filipmu/Bat-Sonar/sonar/Documentation/doxygen/PIT_component.txt

/*!
  \page PIT PIT (Init_PIT)
**          This file implements the PIT (PIT) module initialization
**          according to the Peripheral Initialization settings, and
**          defines interrupt service routines prototypes.
**

- \subpage PIT_settings
- \subpage PIT_regs_overview  
- \subpage PIT_regs_details
- \ref PIT_module "Component documentation" 
\page PIT_regs_overview Registers Initialization Overview
This page contains the initialization values for the registers of the peripheral(s) configured
by the component. 
<table>
<tr><td colspan="4" class="ttitle1">PIT Initialization</td></tr>
<tr><td class="ttitle2">Address</td><td class="ttitle2">Register</td><td class="ttitle2">Register Value</td><td class="ttitle2">Register Description</td></tr>
<tr><td>0x40037000</td><td>PIT_MCR</td>
<td class="regNotResetVal">0x00000000</td>
 <td>PIT_MCR register, peripheral PIT.</td></tr>
<tr><td>0x4003710C</td><td>PIT_TFLG0</td>
<td class="regNotResetVal">0x00000001</td>
 <td>PIT_TFLG0 register, peripheral PIT.</td></tr>
<tr><td>0x4003711C</td><td>PIT_TFLG1</td>
<td class="regNotResetVal">0x00000001</td>
 <td>PIT_TFLG1 register, peripheral PIT.</td></tr>
<tr><td>0x4003712C</td><td>PIT_TFLG2</td>
<td class="regNotResetVal">0x00000001</td>
 <td>PIT_TFLG2 register, peripheral PIT.</td></tr>
<tr><td>0x4003713C</td><td>PIT_TFLG3</td>
<td class="regNotResetVal">0x00000001</td>
 <td>PIT_TFLG3 register, peripheral PIT.</td></tr>
<tr><td>0x40037108</td><td>PIT_TCTRL0</td>
<td class="regNotResetVal">0x00000002</td>
 <td>PIT_TCTRL0 register, peripheral PIT.</td></tr>
<tr><td>0x40037118</td><td>PIT_TCTRL1</td>
<td class="regResetVal">0x00000000</td>
 <td>PIT_TCTRL1 register, peripheral PIT.</td></tr>
<tr><td>0x40037128</td><td>PIT_TCTRL2</td>
<td class="regResetVal">0x00000000</td>
 <td>PIT_TCTRL2 register, peripheral PIT.</td></tr>
<tr><td>0x40037138</td><td>PIT_TCTRL3</td>
<td class="regResetVal">0x00000000</td>
 <td>PIT_TCTRL3 register, peripheral PIT.</td></tr>
<tr><td>0x40037100</td><td>PIT_LDVAL0</td>
<td class="regNotResetVal">0x000003E7</td>
 <td>PIT_LDVAL0 register, peripheral PIT.</td></tr>
<tr><td>0x40037110</td><td>PIT_LDVAL1</td>
<td class="regResetVal">0x00000000</td>
 <td>PIT_LDVAL1 register, peripheral PIT.</td></tr>
<tr><td>0x40037120</td><td>PIT_LDVAL2</td>
<td class="regResetVal">0x00000000</td>
 <td>PIT_LDVAL2 register, peripheral PIT.</td></tr>
<tr><td>0x40037130</td><td>PIT_LDVAL3</td>
<td class="regResetVal">0x00000000</td>
 <td>PIT_LDVAL3 register, peripheral PIT.</td></tr>
</table>
Color Denotes Reset Value
<br/>
\page PIT_regs_details Register Initialization Details
This page contains detailed description of initialization values for the 
registers of the peripheral(s) configured by the component. 

<div class="reghdr1">PIT_MCR</div>
<div class="regdiag">
<table class="regtbl">
<tr class="trd1r">
<td class="trd1c">Bit</td><td>31</td><td>30</td><td>29</td><td>28</td><td>27</td><td>26</td><td>25</td><td>24</td><td>23</td>
<td>22</td><td>21</td><td>20</td><td>19</td><td>18</td><td>17</td><td>16</td>
</tr>
<tr>
<td class="trd1c">R</td><td colspan="1" rowspan="2">-</td><td colspan="1" rowspan="2">-</td><td colspan="1" rowspan="2">-</td>
<td colspan="1" rowspan="2">-</td><td colspan="1" rowspan="2">-</td><td colspan="1" rowspan="2">-</td>
<td colspan="1" rowspan="2">-</td><td colspan="1" rowspan="2">-</td><td colspan="1" rowspan="2">-</td>
<td colspan="1" rowspan="2">-</td><td colspan="1" rowspan="2">-</td><td colspan="1" rowspan="2">-</td>
<td colspan="1" rowspan="2">-</td><td colspan="1" rowspan="2">-</td><td colspan="1" rowspan="2">-</td>
<td colspan="1" rowspan="2">-</td>
</tr>
<tr>
<td class="trd1c">W</td>
</tr>
<tr class="trd1r">
<td class="trd1c">Reset</td><td>0</td><td>0</td><td>0</td><td>0</td><td>0</td><td>0</td><td>0</td><td>0</td><td>0</td><td>0</td>
<td>0</td><td>0</td><td>0</td><td>0</td><td>0</td><td>0</td>
</tr>
</table>
<table class="regtbl">
<tr class="trd1r">
<td class="trd1c">Bit</td><td>15</td><td>14</td><td>13</td><td>12</td><td>11</td><td>10</td><td>9</td><td>8</td><td>7</td>
<td>6</td><td>5</td><td>4</td><td>3</td><td>2</td><td>1</td><td>0</td>
</tr>
<tr>
<td class="trd1c">R</td><td colspan="1" rowspan="2">-</td><td colspan="1" rowspan="2">-</td><td colspan="1" rowspan="2">-</td>
<td colspan="1" rowspan="2">-</td><td colspan="1" rowspan="2">-</td><td colspan="1" rowspan="2">-</td>
<td colspan="1" rowspan="2">-</td><td colspan="1" rowspan="2">-</td><td colspan="1" rowspan="2">-</td>
<td colspan="1" rowspan="2">-</td><td colspan="1" rowspan="2">-</td><td colspan="1" rowspan="2">-</td>
<td colspan="1" rowspan="2">-</td><td colspan="1" rowspan="2">-</td><td colspan="1" rowspan="2">MDIS</td>
<td colspan="1" rowspan="2">FRZ</td>
</tr>
<tr>
<td class="trd1c">W</td>
</tr>
<tr class="trd1r">
<td class="trd1c">Reset</td><td>0</td><td>0</td><td>0</td><td>0</td><td>0</td><td>0</td><td>0</td><td>0</td><td>0</td><td>0</td>
<td>0</td><td>0</td><td>0</td><td>1</td><td>1</td><td>0</td>
</tr>
</table>
        
</div>
<table class="regtbl2"><tr><td class="trowtit" colspan="2">Address</td><td colspan="2">0x40037000</td></tr>
<tr class="trowtit"><td  class="trowtit" colspan="2">Initial value</td><td colspan="2">0x00000000</td></tr>
<tr class="trowtit"><td  class="trowtit" colspan="2">After-reset value</td><td colspan="2">0x00000006</td></tr>
<tr><td class="ttitle2">Bit</td><td class="ttitle2">Field</td><td class="ttitle2">Value</td><td class="ttitle2">Description</td></tr>
<tr><td>1</td><td>MDIS</td><td>0x00</td><td>Module Disable - (PIT section)</td>
<tr><td>0</td><td>FRZ</td><td>0x00</td><td>Freeze</td>
</tr></table>
<div class="reghdr1">PIT_TFLG0</div>
<div class="regdiag">
<table class="regtbl">
<tr class="trd1r">
<td class="trd1c">Bit</td><td>31</td><td>30</td><td>29</td><td>28</td><td>27</td><td>26</td><td>25</td><td>24</td><td>23</td>
<td>22</td><td>21</td><td>20</td><td>19</td><td>18</td><td>17</td><td>16</td>
</tr>
<tr>
<td class="trd1c">R</td><td colspan="1" rowspan="2">-</td><td colspan="1" rowspan="2">-</td><td colspan="1" rowspan="2">-</td>
<td colspan="1" rowspan="2">-</td><td colspan="1" rowspan="2">-</td><td colspan="1" rowspan="2">-</td>
<td colspan="1" rowspan="2">-</td><td colspan="1" rowspan="2">-</td><td colspan="1" rowspan="2">-</td>
<td colspan="1" rowspan="2">-</td><td colspan="1" rowspan="2">-</td><td colspan="1" rowspan="2">-</td>
<td colspan="1" rowspan="2">-</td><td colspan="1" rowspan="2">-</td><td colspan="1" rowspan="2">-</td>
<td colspan="1" rowspan="2">-</td>
</tr>
<tr>
<td class="trd1c">W</td>
</tr>
<tr class="trd1r">
<td class="trd1c">Reset</td><td>0</td><td>0</td><td>0</td><td>0</td><td>0</td><td>0</td><td>0</td><td>0</td><td>0</td><td>0</td>
<td>0</td><td>0</td><td>0</td><td>0</td><td>0</td><td>0</td>
</tr>
</table>
<table class="regtbl">
<tr class="trd1r">
<td class="trd1c">Bit</td><td>15</td><td>14</td><td>13</td><td>12</td><td>11</td><td>10</td><td>9</td><td>8</td><td>7</td>
<td>6</td><td>5</td><td>4</td><td>3</td><td>2</td><td>1</td><td>0</td>
</tr>
<tr>
<td class="trd1c">R</td><td colspan="1" rowspan="2">-</td><td colspan="1" rowspan="2">-</td><td colspan="1" rowspan="2">-</td>
<td colspan="1" rowspan="2">-</td><td colspan="1" rowspan="2">-</td><td colspan="1" rowspan="2">-</td>
<td colspan="1" rowspan="2">-</td><td colspan="1" rowspan="2">-</td><td colspan="1" rowspan="2">-</td>
<td colspan="1" rowspan="2">-</td><td colspan="1" rowspan="2">-</td><td colspan="1" rowspan="2">-</td>
<td colspan="1" rowspan="2">-</td><td colspan="1" rowspan="2">-</td><td colspan="1" rowspan="2">-</td>
<td colspan="1" rowspan="2">TIF</td>
</tr>
<tr>
<td class="trd1c">W</td>
</tr>
<tr class="trd1r">
<td class="trd1c">Reset</td><td>0</td><td>0</td><td>0</td><td>0</td><td>0</td><td>0</td><td>0</td><td>0</td><td>0</td><td>0</td>
<td>0</td><td>0</td><td>0</td><td>0</td><td>0</td><td>0</td>
</tr>
</table>
        
</div>
<table class="regtbl2"><tr><td class="trowtit" colspan="2">Address</td><td colspan="2">0x4003710C</td></tr>
<tr class="trowtit"><td  class="trowtit" colspan="2">Initial value</td><td colspan="2">0x00000001</td></tr>
<tr class="trowtit"><td  class="trowtit" colspan="2">After-reset value</td><td colspan="2">0x00000000</td></tr>
<tr><td class="ttitle2">Bit</td><td class="ttitle2">Field</td><td class="ttitle2">Value</td><td class="ttitle2">Description</td></tr>
<tr><td>0</td><td>TIF</td><td>0x01</td><td>Timer Interrupt Flag</td>
</tr></table>
<div class="reghdr1">PIT_TFLG1</div>
<div class="regdiag">
<table class="regtbl">
<tr class="trd1r">
<td class="trd1c">Bit</td><td>31</td><td>30</td><td>29</td><td>28</td><td>27</td><td>26</td><td>25</td><td>24</td><td>23</td>
<td>22</td><td>21</td><td>20</td><td>19</td><td>18</td><td>17</td><td>16</td>
</tr>
<tr>
<td class="trd1c">R</td><td colspan="1" rowspan="2">-</td><td colspan="1" rowspan="2">-</td><td colspan="1" rowspan="2">-</td>
<td colspan="1" rowspan="2">-</td><td colspan="1" rowspan="2">-</td><td colspan="1" rowspan="2">-</td>
<td colspan="1" rowspan="2">-</td><td colspan="1" rowspan="2">-</td><td colspan="1" rowspan="2">-</td>
<td colspan="1" rowspan="2">-</td><td colspan="1" rowspan="2">-</td><td colspan="1" rowspan="2">-</td>
<td colspan="1" rowspan="2">-</td><td colspan="1" rowspan="2">-</td><td colspan="1" rowspan="2">-</td>
<td colspan="1" rowspan="2">-</td>
</tr>
<tr>
<td class="trd1c">W</td>
</tr>
<tr class="trd1r">
<td class="trd1c">Reset</td><td>0</td><td>0</td><td>0</td><td>0</td><td>0</td><td>0</td><td>0</td><td>0</td><td>0</td><td>0</td>
<td>0</td><td>0</td><td>0</td><td>0</td><td>0</td><td>0</td>
</tr>
</table>
<table class="regtbl">
<tr class="trd1r">
<td class="trd1c">Bit</td><td>15</td><td>14</td><td>13</td><td>12</td><td>11</td><td>10</td><td>9</td><td>8</td><td>7</td>
<td>6</td><td>5</td><td>4</td><td>3</td><td>2</td><td>1</td><td>0</td>
</tr>
<tr>
<td class="trd1c">R</td><td colspan="1" rowspan="2">-</td><td colspan="1" rowspan="2">-</td><td colspan="1" rowspan="2">-</td>
<td colspan="1" rowspan="2">-</td><td colspan="1" rowspan="2">-</td><td colspan="1" rowspan="2">-</td>
<td colspan="1" rowspan="2">-</td><td colspan="1" rowspan="2">-</td><td colspan="1" rowspan="2">-</td>
<td colspan="1" rowspan="2">-</td><td colspan="1" rowspan="2">-</td><td colspan="1" rowspan="2">-</td>
<td colspan="1" rowspan="2">-</td><td colspan="1" rowspan="2">-</td><td colspan="1" rowspan="2">-</td>
<td colspan="1" rowspan="2">TIF</td>
</tr>
<tr>
<td class="trd1c">W</td>
</tr>
<tr class="trd1r">
<td class="trd1c">Reset</td><td>0</td><td>0</td><td>0</td><td>0</td><td>0</td><td>0</td><td>0</td><td>0</td><td>0</td><td>0</td>
<td>0</td><td>0</td><td>0</td><td>0</td><td>0</td><td>0</td>
</tr>
</table>
        
</div>
<table class="regtbl2"><tr><td class="trowtit" colspan="2">Address</td><td colspan="2">0x4003711C</td></tr>
<tr class="trowtit"><td  class="trowtit" colspan="2">Initial value</td><td colspan="2">0x00000001</td></tr>
<tr class="trowtit"><td  class="trowtit" colspan="2">After-reset value</td><td colspan="2">0x00000000</td></tr>
<tr><td class="ttitle2">Bit</td><td class="ttitle2">Field</td><td class="ttitle2">Value</td><td class="ttitle2">Description</td></tr>
<tr><td>0</td><td>TIF</td><td>0x01</td><td>Timer Interrupt Flag</td>
</tr></table>
<div class="reghdr1">PIT_TFLG2</div>
<div class="regdiag">
<table class="regtbl">
<tr class="trd1r">
<td class="trd1c">Bit</td><td>31</td><td>30</td><td>29</td><td>28</td><td>27</td><td>26</td><td>25</td><td>24</td><td>23</td>
<td>22</td><td>21</td><td>20</td><td>19</td><td>18</td><td>17</td><td>16</td>
</tr>
<tr>
<td class="trd1c">R</td><td colspan="1" rowspan="2">-</td><td colspan="1" rowspan="2">-</td><td colspan="1" rowspan="2">-</td>
<td colspan="1" rowspan="2">-</td><td colspan="1" rowspan="2">-</td><td colspan="1" rowspan="2">-</td>
<td colspan="1" rowspan="2">-</td><td colspan="1" rowspan="2">-</td><td colspan="1" rowspan="2">-</td>
<td colspan="1" rowspan="2">-</td><td colspan="1" rowspan="2">-</td><td colspan="1" rowspan="2">-</td>
<td colspan="1" rowspan="2">-</td><td colspan="1" rowspan="2">-</td><td colspan="1" rowspan="2">-</td>
<td colspan="1" rowspan="2">-</td>
</tr>
<tr>
<td class="trd1c">W</td>
</tr>
<tr class="trd1r">
<td class="trd1c">Reset</td><td>0</td><td>0</td><td>0</td><td>0</td><td>0</td><td>0</td><td>0</td><td>0</td><td>0</td><td>0</td>
<td>0</td><td>0</td><td>0</td><td>0</td><td>0</td><td>0</td>
</tr>
</table>
<table class="regtbl">
<tr class="trd1r">
<td class="trd1c">Bit</td><td>15</td><td>14</td><td>13</td><td>12</td><td>11</td><td>10</td><td>9</td><td>8</td><td>7</td>
<td>6</td><td>5</td><td>4</td><td>3</td><td>2</td><td>1</td><td>0</td>
</tr>
<tr>
<td class="trd1c">R</td><td colspan="1" rowspan="2">-</td><td colspan="1" rowspan="2">-</td><td colspan="1" rowspan="2">-</td>
<td colspan="1" rowspan="2">-</td><td colspan="1" rowspan="2">-</td><td colspan="1" rowspan="2">-</td>
<td colspan="1" rowspan="2">-</td><td colspan="1" rowspan="2">-</td><td colspan="1" rowspan="2">-</td>
<td colspan="1" rowspan="2">-</td><td colspan="1" rowspan="2">-</td><td colspan="1" rowspan="2">-</td>
<td colspan="1" rowspan="2">-</td><td colspan="1" rowspan="2">-</td><td colspan="1" rowspan="2">-</td>
<td colspan="1" rowspan="2">TIF</td>
</tr>
<tr>
<td class="trd1c">W</td>
</tr>
<tr class="trd1r">
<td class="trd1c">Reset</td><td>0</td><td>0</td><td>0</td><td>0</td><td>0</td><td>0</td><td>0</td><td>0</td><td>0</td><td>0</td>
<td>0</td><td>0</td><td>0</td><td>0</td><td>0</td><td>0</td>
</tr>
</table>
        
</div>
<table class="regtbl2"><tr><td class="trowtit" colspan="2">Address</td><td colspan="2">0x4003712C</td></tr>
<tr class="trowtit"><td  class="trowtit" colspan="2">Initial value</td><td colspan="2">0x00000001</td></tr>
<tr class="trowtit"><td  class="trowtit" colspan="2">After-reset value</td><td colspan="2">0x00000000</td></tr>
<tr><td class="ttitle2">Bit</td><td class="ttitle2">Field</td><td class="ttitle2">Value</td><td class="ttitle2">Description</td></tr>
<tr><td>0</td><td>TIF</td><td>0x01</td><td>Timer Interrupt Flag</td>
</tr></table>
<div class="reghdr1">PIT_TFLG3</div>
<div class="regdiag">
<table class="regtbl">
<tr class="trd1r">
<td class="trd1c">Bit</td><td>31</td><td>30</td><td>29</td><td>28</td><td>27</td><td>26</td><td>25</td><td>24</td><td>23</td>
<td>22</td><td>21</td><td>20</td><td>19</td><td>18</td><td>17</td><td>16</td>
</tr>
<tr>
<td class="trd1c">R</td><td colspan="1" rowspan="2">-</td><td colspan="1" rowspan="2">-</td><td colspan="1" rowspan="2">-</td>
<td colspan="1" rowspan="2">-</td><td colspan="1" rowspan="2">-</td><td colspan="1" rowspan="2">-</td>
<td colspan="1" rowspan="2">-</td><td colspan="1" rowspan="2">-</td><td colspan="1" rowspan="2">-</td>
<td colspan="1" rowspan="2">-</td><td colspan="1" rowspan="2">-</td><td colspan="1" rowspan="2">-</td>
<td colspan="1" rowspan="2">-</td><td colspan="1" rowspan="2">-</td><td colspan="1" rowspan="2">-</td>
<td colspan="1" rowspan="2">-</td>
</tr>
<tr>
<td class="trd1c">W</td>
</tr>
<tr class="trd1r">
<td class="trd1c">Reset</td><td>0</td><td>0</td><td>0</td><td>0</td><td>0</td><td>0</td><td>0</td><td>0</td><td>0</td><td>0</td>
<td>0</td><td>0</td><td>0</td><td>0</td><td>0</td><td>0</td>
</tr>
</table>
<table class="regtbl">
<tr class="trd1r">
<td class="trd1c">Bit</td><td>15</td><td>14</td><td>13</td><td>12</td><td>11</td><td>10</td><td>9</td><td>8</td><td>7</td>
<td>6</td><td>5</td><td>4</td><td>3</td><td>2</td><td>1</td><td>0</td>
</tr>
<tr>
<td class="trd1c">R</td><td colspan="1" rowspan="2">-</td><td colspan="1" rowspan="2">-</td><td colspan="1" rowspan="2">-</td>
<td colspan="1" rowspan="2">-</td><td colspan="1" rowspan="2">-</td><td colspan="1" rowspan="2">-</td>
<td colspan="1" rowspan="2">-</td><td colspan="1" rowspan="2">-</td><td colspan="1" rowspan="2">-</td>
<td colspan="1" rowspan="2">-</td><td colspan="1" rowspan="2">-</td><td colspan="1" rowspan="2">-</td>
<td colspan="1" rowspan="2">-</td><td colspan="1" rowspan="2">-</td><td colspan="1" rowspan="2">-</td>
<td colspan="1" rowspan="2">TIF</td>
</tr>
<tr>
<td class="trd1c">W</td>
</tr>
<tr class="trd1r">
<td class="trd1c">Reset</td><td>0</td><td>0</td><td>0</td><td>0</td><td>0</td><td>0</td><td>0</td><td>0</td><td>0</td><td>0</td>
<td>0</td><td>0</td><td>0</td><td>0</td><td>0</td><td>0</td>
</tr>
</table>
        
</div>
<table class="regtbl2"><tr><td class="trowtit" colspan="2">Address</td><td colspan="2">0x4003713C</td></tr>
<tr class="trowtit"><td  class="trowtit" colspan="2">Initial value</td><td colspan="2">0x00000001</td></tr>
<tr class="trowtit"><td  class="trowtit" colspan="2">After-reset value</td><td colspan="2">0x00000000</td></tr>
<tr><td class="ttitle2">Bit</td><td class="ttitle2">Field</td><td class="ttitle2">Value</td><td class="ttitle2">Description</td></tr>
<tr><td>0</td><td>TIF</td><td>0x01</td><td>Timer Interrupt Flag</td>
</tr></table>
<div class="reghdr1">PIT_TCTRL0</div>
<div class="regdiag">
<table class="regtbl">
<tr class="trd1r">
<td class="trd1c">Bit</td><td>31</td><td>30</td><td>29</td><td>28</td><td>27</td><td>26</td><td>25</td><td>24</td><td>23</td>
<td>22</td><td>21</td><td>20</td><td>19</td><td>18</td><td>17</td><td>16</td>
</tr>
<tr>
<td class="trd1c">R</td><td colspan="1" rowspan="2">-</td><td colspan="1" rowspan="2">-</td><td colspan="1" rowspan="2">-</td>
<td colspan="1" rowspan="2">-</td><td colspan="1" rowspan="2">-</td><td colspan="1" rowspan="2">-</td>
<td colspan="1" rowspan="2">-</td><td colspan="1" rowspan="2">-</td><td colspan="1" rowspan="2">-</td>
<td colspan="1" rowspan="2">-</td><td colspan="1" rowspan="2">-</td><td colspan="1" rowspan="2">-</td>
<td colspan="1" rowspan="2">-</td><td colspan="1" rowspan="2">-</td><td colspan="1" rowspan="2">-</td>
<td colspan="1" rowspan="2">-</td>
</tr>
<tr>
<td class="trd1c">W</td>
</tr>
<tr class="trd1r">
<td class="trd1c">Reset</td><td>0</td><td>0</td><td>0</td><td>0</td><td>0</td><td>0</td><td>0</td><td>0</td><td>0</td><td>0</td>
<td>0</td><td>0</td><td>0</td><td>0</td><td>0</td><td>0</td>
</tr>
</table>
<table class="regtbl">
<tr class="trd1r">
<td class="trd1c">Bit</td><td>15</td><td>14</td><td>13</td><td>12</td><td>11</td><td>10</td><td>9</td><td>8</td><td>7</td>
<td>6</td><td>5</td><td>4</td><td>3</td><td>2</td><td>1</td><td>0</td>
</tr>
<tr>
<td class="trd1c">R</td><td colspan="1" rowspan="2">-</td><td colspan="1" rowspan="2">-</td><td colspan="1" rowspan="2">-</td>
<td colspan="1" rowspan="2">-</td><td colspan="1" rowspan="2">-</td><td colspan="1" rowspan="2">-</td>
<td colspan="1" rowspan="2">-</td><td colspan="1" rowspan="2">-</td><td colspan="1" rowspan="2">-</td>
<td colspan="1" rowspan="2">-</td><td colspan="1" rowspan="2">-</td><td colspan="1" rowspan="2">-</td>
<td colspan="1" rowspan="2">-</td><td colspan="1" rowspan="2">CHN</td><td colspan="1" rowspan="2">TIE</td>
<td colspan="1" rowspan="2">TEN</td>
</tr>
<tr>
<td class="trd1c">W</td>
</tr>
<tr class="trd1r">
<td class="trd1c">Reset</td><td>0</td><td>0</td><td>0</td><td>0</td><td>0</td><td>0</td><td>0</td><td>0</td><td>0</td><td>0</td>
<td>0</td><td>0</td><td>0</td><td>0</td><td>0</td><td>0</td>
</tr>
</table>
        
</div>
<table class="regtbl2"><tr><td class="trowtit" colspan="2">Address</td><td colspan="2">0x40037108</td></tr>
<tr class="trowtit"><td  class="trowtit" colspan="2">Initial value</td><td colspan="2">0x00000002</td></tr>
<tr class="trowtit"><td  class="trowtit" colspan="2">After-reset value</td><td colspan="2">0x00000000</td></tr>
<tr><td class="ttitle2">Bit</td><td class="ttitle2">Field</td><td class="ttitle2">Value</td><td class="ttitle2">Description</td></tr>
<tr><td>2</td><td>CHN</td><td>0x00</td><td>Chain Mode</td>
<tr><td>1</td><td>TIE</td><td>0x01</td><td>Timer Interrupt Enable</td>
<tr><td>0</td><td>TEN</td><td>0x00</td><td>Timer Enable</td>
</tr></table>
<div class="reghdr1">PIT_TCTRL1</div>
<div class="regdiag">
<table class="regtbl">
<tr class="trd1r">
<td class="trd1c">Bit</td><td>31</td><td>30</td><td>29</td><td>28</td><td>27</td><td>26</td><td>25</td><td>24</td><td>23</td>
<td>22</td><td>21</td><td>20</td><td>19</td><td>18</td><td>17</td><td>16</td>
</tr>
<tr>
<td class="trd1c">R</td><td colspan="1" rowspan="2">-</td><td colspan="1" rowspan="2">-</td><td colspan="1" rowspan="2">-</td>
<td colspan="1" rowspan="2">-</td><td colspan="1" rowspan="2">-</td><td colspan="1" rowspan="2">-</td>
<td colspan="1" rowspan="2">-</td><td colspan="1" rowspan="2">-</td><td colspan="1" rowspan="2">-</td>
<td colspan="1" rowspan="2">-</td><td colspan="1" rowspan="2">-</td><td colspan="1" rowspan="2">-</td>
<td colspan="1" rowspan="2">-</td><td colspan="1" rowspan="2">-</td><td colspan="1" rowspan="2">-</td>
<td colspan="1" rowspan="2">-</td>
</tr>
<tr>
<td class="trd1c">W</td>
</tr>
<tr class="trd1r">
<td class="trd1c">Reset</td><td>0</td><td>0</td><td>0</td><td>0</td><td>0</td><td>0</td><td>0</td><td>0</td><td>0</td><td>0</td>
<td>0</td><td>0</td><td>0</td><td>0</td><td>0</td><td>0</td>
</tr>
</table>
<table class="regtbl">
<tr class="trd1r">
<td class="trd1c">Bit</td><td>15</td><td>14</td><td>13</td><td>12</td><td>11</td><td>10</td><td>9</td><td>8</td><td>7</td>
<td>6</td><td>5</td><td>4</td><td>3</td><td>2</td><td>1</td><td>0</td>
</tr>
<tr>
<td class="trd1c">R</td><td colspan="1" rowspan="2">-</td><td colspan="1" rowspan="2">-</td><td colspan="1" rowspan="2">-</td>
<td colspan="1" rowspan="2">-</td><td colspan="1" rowspan="2">-</td><td colspan="1" rowspan="2">-</td>
<td colspan="1" rowspan="2">-</td><td colspan="1" rowspan="2">-</td><td colspan="1" rowspan="2">-</td>
<td colspan="1" rowspan="2">-</td><td colspan="1" rowspan="2">-</td><td colspan="1" rowspan="2">-</td>
<td colspan="1" rowspan="2">-</td><td colspan="1" rowspan="2">CHN</td><td colspan="1" rowspan="2">TIE</td>
<td colspan="1" rowspan="2">TEN</td>
</tr>
<tr>
<td class="trd1c">W</td>
</tr>
<tr class="trd1r">
<td class="trd1c">Reset</td><td>0</td><td>0</td><td>0</td><td>0</td><td>0</td><td>0</td><td>0</td><td>0</td><td>0</td><td>0</td>
<td>0</td><td>0</td><td>0</td><td>0</td><td>0</td><td>0</td>
</tr>
</table>
        
</div>
<table class="regtbl2"><tr><td class="trowtit" colspan="2">Address</td><td colspan="2">0x40037118</td></tr>
<tr class="trowtit"><td  class="trowtit" colspan="2">Initial value</td><td colspan="2">0x00000000</td></tr>
<tr class="trowtit"><td  class="trowtit" colspan="2">After-reset value</td><td colspan="2">0x00000000</td></tr>
<tr><td class="ttitle2">Bit</td><td class="ttitle2">Field</td><td class="ttitle2">Value</td><td class="ttitle2">Description</td></tr>
<tr><td>2</td><td>CHN</td><td>0x00</td><td>Chain Mode</td>
<tr><td>1</td><td>TIE</td><td>0x00</td><td>Timer Interrupt Enable</td>
<tr><td>0</td><td>TEN</td><td>0x00</td><td>Timer Enable</td>
</tr></table>
<div class="reghdr1">PIT_TCTRL2</div>
<div class="regdiag">
<table class="regtbl">
<tr class="trd1r">
<td class="trd1c">Bit</td><td>31</td><td>30</td><td>29</td><td>28</td><td>27</td><td>26</td><td>25</td><td>24</td><td>23</td>
<td>22</td><td>21</td><td>20</td><td>19</td><td>18</td><td>17</td><td>16</td>
</tr>
<tr>
<td class="trd1c">R</td><td colspan="1" rowspan="2">-</td><td colspan="1" rowspan="2">-</td><td colspan="1" rowspan="2">-</td>
<td colspan="1" rowspan="2">-</td><td colspan="1" rowspan="2">-</td><td colspan="1" rowspan="2">-</td>
<td colspan="1" rowspan="2">-</td><td colspan="1" rowspan="2">-</td><td colspan="1" rowspan="2">-</td>
<td colspan="1" rowspan="2">-</td><td colspan="1" rowspan="2">-</td><td colspan="1" rowspan="2">-</td>
<td colspan="1" rowspan="2">-</td><td colspan="1" rowspan="2">-</td><td colspan="1" rowspan="2">-</td>
<td colspan="1" rowspan="2">-</td>
</tr>
<tr>
<td class="trd1c">W</td>
</tr>
<tr class="trd1r">
<td class="trd1c">Reset</td><td>0</td><td>0</td><td>0</td><td>0</td><td>0</td><td>0</td><td>0</td><td>0</td><td>0</td><td>0</td>
<td>0</td><td>0</td><td>0</td><td>0</td><td>0</td><td>0</td>
</tr>
</table>
<table class="regtbl">
<tr class="trd1r">
<td class="trd1c">Bit</td><td>15</td><td>14</td><td>13</td><td>12</td><td>11</td><td>10</td><td>9</td><td>8</td><td>7</td>
<td>6</td><td>5</td><td>4</td><td>3</td><td>2</td><td>1</td><td>0</td>
</tr>
<tr>
<td class="trd1c">R</td><td colspan="1" rowspan="2">-</td><td colspan="1" rowspan="2">-</td><td colspan="1" rowspan="2">-</td>
<td colspan="1" rowspan="2">-</td><td colspan="1" rowspan="2">-</td><td colspan="1" rowspan="2">-</td>
<td colspan="1" rowspan="2">-</td><td colspan="1" rowspan="2">-</td><td colspan="1" rowspan="2">-</td>
<td colspan="1" rowspan="2">-</td><td colspan="1" rowspan="2">-</td><td colspan="1" rowspan="2">-</td>
<td colspan="1" rowspan="2">-</td><td colspan="1" rowspan="2">CHN</td><td colspan="1" rowspan="2">TIE</td>
<td colspan="1" rowspan="2">TEN</td>
</tr>
<tr>
<td class="trd1c">W</td>
</tr>
<tr class="trd1r">
<td class="trd1c">Reset</td><td>0</td><td>0</td><td>0</td><td>0</td><td>0</td><td>0</td><td>0</td><td>0</td><td>0</td><td>0</td>
<td>0</td><td>0</td><td>0</td><td>0</td><td>0</td><td>0</td>
</tr>
</table>
        
</div>
<table class="regtbl2"><tr><td class="trowtit" colspan="2">Address</td><td colspan="2">0x40037128</td></tr>
<tr class="trowtit"><td  class="trowtit" colspan="2">Initial value</td><td colspan="2">0x00000000</td></tr>
<tr class="trowtit"><td  class="trowtit" colspan="2">After-reset value</td><td colspan="2">0x00000000</td></tr>
<tr><td class="ttitle2">Bit</td><td class="ttitle2">Field</td><td class="ttitle2">Value</td><td class="ttitle2">Description</td></tr>
<tr><td>2</td><td>CHN</td><td>0x00</td><td>Chain Mode</td>
<tr><td>1</td><td>TIE</td><td>0x00</td><td>Timer Interrupt Enable</td>
<tr><td>0</td><td>TEN</td><td>0x00</td><td>Timer Enable</td>
</tr></table>
<div class="reghdr1">PIT_TCTRL3</div>
<div class="regdiag">
<table class="regtbl">
<tr class="trd1r">
<td class="trd1c">Bit</td><td>31</td><td>30</td><td>29</td><td>28</td><td>27</td><td>26</td><td>25</td><td>24</td><td>23</td>
<td>22</td><td>21</td><td>20</td><td>19</td><td>18</td><td>17</td><td>16</td>
</tr>
<tr>
<td class="trd1c">R</td><td colspan="1" rowspan="2">-</td><td colspan="1" rowspan="2">-</td><td colspan="1" rowspan="2">-</td>
<td colspan="1" rowspan="2">-</td><td colspan="1" rowspan="2">-</td><td colspan="1" rowspan="2">-</td>
<td colspan="1" rowspan="2">-</td><td colspan="1" rowspan="2">-</td><td colspan="1" rowspan="2">-</td>
<td colspan="1" rowspan="2">-</td><td colspan="1" rowspan="2">-</td><td colspan="1" rowspan="2">-</td>
<td colspan="1" rowspan="2">-</td><td colspan="1" rowspan="2">-</td><td colspan="1" rowspan="2">-</td>
<td colspan="1" rowspan="2">-</td>
</tr>
<tr>
<td class="trd1c">W</td>
</tr>
<tr class="trd1r">
<td class="trd1c">Reset</td><td>0</td><td>0</td><td>0</td><td>0</td><td>0</td><td>0</td><td>0</td><td>0</td><td>0</td><td>0</td>
<td>0</td><td>0</td><td>0</td><td>0</td><td>0</td><td>0</td>
</tr>
</table>
<table class="regtbl">
<tr class="trd1r">
<td class="trd1c">Bit</td><td>15</td><td>14</td><td>13</td><td>12</td><td>11</td><td>10</td><td>9</td><td>8</td><td>7</td>
<td>6</td><td>5</td><td>4</td><td>3</td><td>2</td><td>1</td><td>0</td>
</tr>
<tr>
<td class="trd1c">R</td><td colspan="1" rowspan="2">-</td><td colspan="1" rowspan="2">-</td><td colspan="1" rowspan="2">-</td>
<td colspan="1" rowspan="2">-</td><td colspan="1" rowspan="2">-</td><td colspan="1" rowspan="2">-</td>
<td colspan="1" rowspan="2">-</td><td colspan="1" rowspan="2">-</td><td colspan="1" rowspan="2">-</td>
<td colspan="1" rowspan="2">-</td><td colspan="1" rowspan="2">-</td><td colspan="1" rowspan="2">-</td>
<td colspan="1" rowspan="2">-</td><td colspan="1" rowspan="2">CHN</td><td colspan="1" rowspan="2">TIE</td>
<td colspan="1" rowspan="2">TEN</td>
</tr>
<tr>
<td class="trd1c">W</td>
</tr>
<tr class="trd1r">
<td class="trd1c">Reset</td><td>0</td><td>0</td><td>0</td><td>0</td><td>0</td><td>0</td><td>0</td><td>0</td><td>0</td><td>0</td>
<td>0</td><td>0</td><td>0</td><td>0</td><td>0</td><td>0</td>
</tr>
</table>
        
</div>
<table class="regtbl2"><tr><td class="trowtit" colspan="2">Address</td><td colspan="2">0x40037138</td></tr>
<tr class="trowtit"><td  class="trowtit" colspan="2">Initial value</td><td colspan="2">0x00000000</td></tr>
<tr class="trowtit"><td  class="trowtit" colspan="2">After-reset value</td><td colspan="2">0x00000000</td></tr>
<tr><td class="ttitle2">Bit</td><td class="ttitle2">Field</td><td class="ttitle2">Value</td><td class="ttitle2">Description</td></tr>
<tr><td>2</td><td>CHN</td><td>0x00</td><td>Chain Mode</td>
<tr><td>1</td><td>TIE</td><td>0x00</td><td>Timer Interrupt Enable</td>
<tr><td>0</td><td>TEN</td><td>0x00</td><td>Timer Enable</td>
</tr></table>
<div class="reghdr1">PIT_LDVAL0</div>
<div class="regdiag">
<table class="regtbl">
<tr class="trd1r">
<td class="trd1c">Bit</td><td>31</td><td>30</td><td>29</td><td>28</td><td>27</td><td>26</td><td>25</td><td>24</td><td>23</td>
<td>22</td><td>21</td><td>20</td><td>19</td><td>18</td><td>17</td><td>16</td>
</tr>
<tr>
<td class="trd1c">R</td><td colspan="16" rowspan="2">TSV</td>
</tr>
<tr>
<td class="trd1c">W</td>
</tr>
<tr class="trd1r">
<td class="trd1c">Reset</td><td>0</td><td>0</td><td>0</td><td>0</td><td>0</td><td>0</td><td>0</td><td>0</td><td>0</td><td>0</td>
<td>0</td><td>0</td><td>0</td><td>0</td><td>0</td><td>0</td>
</tr>
</table>
<table class="regtbl">
<tr class="trd1r">
<td class="trd1c">Bit</td><td>15</td><td>14</td><td>13</td><td>12</td><td>11</td><td>10</td><td>9</td><td>8</td><td>7</td>
<td>6</td><td>5</td><td>4</td><td>3</td><td>2</td><td>1</td><td>0</td>
</tr>
<tr>
<td class="trd1c">R</td><td colspan="32" rowspan="2">TSV</td>
</tr>
<tr>
<td class="trd1c">W</td>
</tr>
<tr class="trd1r">
<td class="trd1c">Reset</td><td>0</td><td>0</td><td>0</td><td>0</td><td>0</td><td>0</td><td>0</td><td>0</td><td>0</td><td>0</td>
<td>0</td><td>0</td><td>0</td><td>0</td><td>0</td><td>0</td>
</tr>
</table>
        
</div>
<table class="regtbl2"><tr><td class="trowtit" colspan="2">Address</td><td colspan="2">0x40037100</td></tr>
<tr class="trowtit"><td  class="trowtit" colspan="2">Initial value</td><td colspan="2">0x000003E7</td></tr>
<tr class="trowtit"><td  class="trowtit" colspan="2">After-reset value</td><td colspan="2">0x00000000</td></tr>
<tr><td class="ttitle2">Bit</td><td class="ttitle2">Field</td><td class="ttitle2">Value</td><td class="ttitle2">Description</td></tr>
<tr><td>0 - 31</td><td>TSV</td><td>0x00</td><td>Timer Start Value</td>
</tr></table>
<div class="reghdr1">PIT_LDVAL1</div>
<div class="regdiag">
<table class="regtbl">
<tr class="trd1r">
<td class="trd1c">Bit</td><td>31</td><td>30</td><td>29</td><td>28</td><td>27</td><td>26</td><td>25</td><td>24</td><td>23</td>
<td>22</td><td>21</td><td>20</td><td>19</td><td>18</td><td>17</td><td>16</td>
</tr>
<tr>
<td class="trd1c">R</td><td colspan="16" rowspan="2">TSV</td>
</tr>
<tr>
<td class="trd1c">W</td>
</tr>
<tr class="trd1r">
<td class="trd1c">Reset</td><td>0</td><td>0</td><td>0</td><td>0</td><td>0</td><td>0</td><td>0</td><td>0</td><td>0</td><td>0</td>
<td>0</td><td>0</td><td>0</td><td>0</td><td>0</td><td>0</td>
</tr>
</table>
<table class="regtbl">
<tr class="trd1r">
<td class="trd1c">Bit</td><td>15</td><td>14</td><td>13</td><td>12</td><td>11</td><td>10</td><td>9</td><td>8</td><td>7</td>
<td>6</td><td>5</td><td>4</td><td>3</td><td>2</td><td>1</td><td>0</td>
</tr>
<tr>
<td class="trd1c">R</td><td colspan="32" rowspan="2">TSV</td>
</tr>
<tr>
<td class="trd1c">W</td>
</tr>
<tr class="trd1r">
<td class="trd1c">Reset</td><td>0</td><td>0</td><td>0</td><td>0</td><td>0</td><td>0</td><td>0</td><td>0</td><td>0</td><td>0</td>
<td>0</td><td>0</td><td>0</td><td>0</td><td>0</td><td>0</td>
</tr>
</table>
        
</div>
<table class="regtbl2"><tr><td class="trowtit" colspan="2">Address</td><td colspan="2">0x40037110</td></tr>
<tr class="trowtit"><td  class="trowtit" colspan="2">Initial value</td><td colspan="2">0x00000000</td></tr>
<tr class="trowtit"><td  class="trowtit" colspan="2">After-reset value</td><td colspan="2">0x00000000</td></tr>
<tr><td class="ttitle2">Bit</td><td class="ttitle2">Field</td><td class="ttitle2">Value</td><td class="ttitle2">Description</td></tr>
<tr><td>0 - 31</td><td>TSV</td><td>0x00</td><td>Timer Start Value</td>
</tr></table>
<div class="reghdr1">PIT_LDVAL2</div>
<div class="regdiag">
<table class="regtbl">
<tr class="trd1r">
<td class="trd1c">Bit</td><td>31</td><td>30</td><td>29</td><td>28</td><td>27</td><td>26</td><td>25</td><td>24</td><td>23</td>
<td>22</td><td>21</td><td>20</td><td>19</td><td>18</td><td>17</td><td>16</td>
</tr>
<tr>
<td class="trd1c">R</td><td colspan="16" rowspan="2">TSV</td>
</tr>
<tr>
<td class="trd1c">W</td>
</tr>
<tr class="trd1r">
<td class="trd1c">Reset</td><td>0</td><td>0</td><td>0</td><td>0</td><td>0</td><td>0</td><td>0</td><td>0</td><td>0</td><td>0</td>
<td>0</td><td>0</td><td>0</td><td>0</td><td>0</td><td>0</td>
</tr>
</table>
<table class="regtbl">
<tr class="trd1r">
<td class="trd1c">Bit</td><td>15</td><td>14</td><td>13</td><td>12</td><td>11</td><td>10</td><td>9</td><td>8</td><td>7</td>
<td>6</td><td>5</td><td>4</td><td>3</td><td>2</td><td>1</td><td>0</td>
</tr>
<tr>
<td class="trd1c">R</td><td colspan="32" rowspan="2">TSV</td>
</tr>
<tr>
<td class="trd1c">W</td>
</tr>
<tr class="trd1r">
<td class="trd1c">Reset</td><td>0</td><td>0</td><td>0</td><td>0</td><td>0</td><td>0</td><td>0</td><td>0</td><td>0</td><td>0</td>
<td>0</td><td>0</td><td>0</td><td>0</td><td>0</td><td>0</td>
</tr>
</table>
        
</div>
<table class="regtbl2"><tr><td class="trowtit" colspan="2">Address</td><td colspan="2">0x40037120</td></tr>
<tr class="trowtit"><td  class="trowtit" colspan="2">Initial value</td><td colspan="2">0x00000000</td></tr>
<tr class="trowtit"><td  class="trowtit" colspan="2">After-reset value</td><td colspan="2">0x00000000</td></tr>
<tr><td class="ttitle2">Bit</td><td class="ttitle2">Field</td><td class="ttitle2">Value</td><td class="ttitle2">Description</td></tr>
<tr><td>0 - 31</td><td>TSV</td><td>0x00</td><td>Timer Start Value</td>
</tr></table>
<div class="reghdr1">PIT_LDVAL3</div>
<div class="regdiag">
<table class="regtbl">
<tr class="trd1r">
<td class="trd1c">Bit</td><td>31</td><td>30</td><td>29</td><td>28</td><td>27</td><td>26</td><td>25</td><td>24</td><td>23</td>
<td>22</td><td>21</td><td>20</td><td>19</td><td>18</td><td>17</td><td>16</td>
</tr>
<tr>
<td class="trd1c">R</td><td colspan="16" rowspan="2">TSV</td>
</tr>
<tr>
<td class="trd1c">W</td>
</tr>
<tr class="trd1r">
<td class="trd1c">Reset</td><td>0</td><td>0</td><td>0</td><td>0</td><td>0</td><td>0</td><td>0</td><td>0</td><td>0</td><td>0</td>
<td>0</td><td>0</td><td>0</td><td>0</td><td>0</td><td>0</td>
</tr>
</table>
<table class="regtbl">
<tr class="trd1r">
<td class="trd1c">Bit</td><td>15</td><td>14</td><td>13</td><td>12</td><td>11</td><td>10</td><td>9</td><td>8</td><td>7</td>
<td>6</td><td>5</td><td>4</td><td>3</td><td>2</td><td>1</td><td>0</td>
</tr>
<tr>
<td class="trd1c">R</td><td colspan="32" rowspan="2">TSV</td>
</tr>
<tr>
<td class="trd1c">W</td>
</tr>
<tr class="trd1r">
<td class="trd1c">Reset</td><td>0</td><td>0</td><td>0</td><td>0</td><td>0</td><td>0</td><td>0</td><td>0</td><td>0</td><td>0</td>
<td>0</td><td>0</td><td>0</td><td>0</td><td>0</td><td>0</td>
</tr>
</table>
        
</div>
<table class="regtbl2"><tr><td class="trowtit" colspan="2">Address</td><td colspan="2">0x40037130</td></tr>
<tr class="trowtit"><td  class="trowtit" colspan="2">Initial value</td><td colspan="2">0x00000000</td></tr>
<tr class="trowtit"><td  class="trowtit" colspan="2">After-reset value</td><td colspan="2">0x00000000</td></tr>
<tr><td class="ttitle2">Bit</td><td class="ttitle2">Field</td><td class="ttitle2">Value</td><td class="ttitle2">Description</td></tr>
<tr><td>0 - 31</td><td>TSV</td><td>0x00</td><td>Timer Start Value</td>
</tr></table>
*/
/*!
\page PIT_settings Component Settings
\code
**          Component name                                 : PIT
**          Device                                         : PIT
**          Setttings                                      : 
**            Clock gate                                   : Enabled
**            Clock settings                               : 
**              Base clock frequency                       : 60 MHz
**            Freeze in debug mode                         : no
**          Channels                                       : 
**            Channel 0                                    : 
**              Timer 0                                    : Disabled
**              Timer 0 load value                         : 999
**              Timer 0 Period                             : 16.667 us
**              Interrupt                                  : 
**                Interrupt                                : INT_PIT0
**                Interrupt request                        : Enabled
**                Interrupt priority                       : 16
**                ISR Name                                 : PIT0_Int
**                Timer interrupt                          : Enabled
**            Channel 1                                    : 
**              Timer 1                                    : Disabled
**              Timer 1 chain mode                         : Disabled
**              Timer 1 load value                         : 0
**              Timer 1 Period                             : 0.017 us
**              Interrupt                                  : 
**                Interrupt                                : INT_PIT1
**                Interrupt request                        : <Automatic>
**                Interrupt priority                       : <Automatic>
**                ISR Name                                 : 
**                Timer interrupt                          : Disabled
**            Channel 2                                    : 
**              Timer 2                                    : Disabled
**              Timer 2 chain mode                         : Disabled
**              Timer 2 load value                         : 0
**              Timer 2 Period                             : 0.017 us
**              Interrupt                                  : 
**                Interrupt                                : INT_PIT2
**                Interrupt request                        : <Automatic>
**                Interrupt priority                       : <Automatic>
**                ISR Name                                 : 
**                Timer interrupt                          : Disabled
**            Channel 3                                    : 
**              Timer 3                                    : Disabled
**              Timer 3 chain mode                         : Disabled
**              Timer 3 load value                         : 0
**              Timer 3 Period                             : 0.017 us
**              Interrupt                                  : 
**                Interrupt                                : INT_PIT3
**                Interrupt request                        : <Automatic>
**                Interrupt priority                       : <Automatic>
**                ISR Name                                 : 
**                Timer interrupt                          : Disabled
**          Initialization                                 : 
**            Module                                       : Enabled
**            Call Init method                             : yes
**            Utilize after reset values                   : default
<h1>
\endcode
*/
